bplaat/rescuebot/include/website.hpp

unsigned char src_website_html[] = {
  0x3c, 0x21, 0x44, 0x4f, 0x43, 0x54, 0x59, 0x50, 0x45, 0x20, 0x68, 0x74,
  0x6d, 0x6c, 0x3e, 0x0d, 0x0a, 0x3c, 0x68, 0x74, 0x6d, 0x6c, 0x20, 0x6c,
  0x61, 0x6e, 0x67, 0x3d, 0x22, 0x65, 0x6e, 0x22, 0x3e, 0x0d, 0x0a, 0x3c,
  0x68, 0x65, 0x61, 0x64, 0x3e, 0x0d, 0x0a, 0x20, 0x20, 0x20, 0x20, 0x3c,
  0x6d, 0x65, 0x74, 0x61, 0x20, 0x63, 0x68, 0x61, 0x72, 0x73, 0x65, 0x74,
  0x3d, 0x22, 0x55, 0x54, 0x46, 0x2d, 0x38, 0x22, 0x3e, 0x0d, 0x0a, 0x20,
  0x20, 0x20, 0x20, 0x3c, 0x6d, 0x65, 0x74, 0x61, 0x20, 0x6e, 0x61, 0x6d,
  0x65, 0x3d, 0x22, 0x76, 0x69, 0x65, 0x77, 0x70, 0x6f, 0x72, 0x74, 0x22,
  0x20, 0x63, 0x6f, 0x6e, 0x74, 0x65, 0x6e, 0x74, 0x3d, 0x22, 0x77, 0x69,
  0x64, 0x74, 0x68, 0x3d, 0x64, 0x65, 0x76, 0x69, 0x63, 0x65, 0x2d, 0x77,
  0x69, 0x64, 0x74, 0x68, 0x2c, 0x20, 0x69, 0x6e, 0x69, 0x74, 0x69, 0x61,
  0x6c, 0x2d, 0x73, 0x63, 0x61, 0x6c, 0x65, 0x3d, 0x31, 0x2e, 0x30, 0x2c,
  0x20, 0x6d, 0x69, 0x6e, 0x69, 0x6d, 0x75, 0x6d, 0x2d, 0x73, 0x63, 0x61,
  0x6c, 0x65, 0x3d, 0x31, 0x2e, 0x30, 0x2c, 0x20, 0x6d, 0x61, 0x78, 0x69,
  0x6d, 0x75, 0x6d, 0x2d, 0x73, 0x63, 0x61, 0x6c, 0x65, 0x3d, 0x31, 0x2e,
  0x30, 0x2c, 0x20, 0x75, 0x73, 0x65, 0x72, 0x2d, 0x73, 0x63, 0x61, 0x6c,
  0x61, 0x62, 0x6c, 0x65, 0x3d, 0x6e, 0x6f, 0x22, 0x3e, 0x0d, 0x0a, 0x20,
  0x20, 0x20, 0x20, 0x3c, 0x74, 0x69, 0x74, 0x6c, 0x65, 0x3e, 0x52, 0x65,
  0x73, 0x63, 0x75, 0x65, 0x42, 0x6f, 0x74, 0x3c, 0x2f, 0x74, 0x69, 0x74,
  0x6c, 0x65, 0x3e, 0x0d, 0x0a, 0x20, 0x20, 0x20, 0x20, 0x3c, 0x73, 0x74,
  0x79, 0x6c, 0x65, 0x3e, 0x0d, 0x0a, 0x20, 0x20, 0x20, 0x20, 0x20, 0x20,
  0x20, 0x20, 0x68, 0x74, 0x6d, 0x6c, 0x2c, 0x2e, 0x72, 0x6f, 0x6f, 0x74,
  0x7b, 0x68, 0x65, 0x69, 0x67, 0x68, 0x74, 0x3a, 0x31, 0x30, 0x30, 0x25,
  0x7d, 0x62, 0x6f, 0x64, 0x79, 0x7b, 0x6d, 0x61, 0x72, 0x67, 0x69, 0x6e,
  0x3a, 0x30, 0x3b, 0x68, 0x65, 0x69, 0x67, 0x68, 0x74, 0x3a, 0x31, 0x30,
  0x30, 0x25, 0x3b, 0x63, 0x6f, 0x6c, 0x6f, 0x72, 0x3a, 0x23, 0x31, 0x31,
  0x31, 0x3b, 0x62, 0x61, 0x63, 0x6b, 0x67, 0x72, 0x6f, 0x75, 0x6e, 0x64,
  0x2d, 0x63, 0x6f, 0x6c, 0x6f, 0x72, 0x3a, 0x23, 0x66, 0x66, 0x66, 0x3b,
  0x75, 0x73, 0x65, 0x72, 0x2d, 0x73, 0x65, 0x6c, 0x65, 0x63, 0x74, 0x3a,
  0x6e, 0x6f, 0x6e, 0x65, 0x3b, 0x63, 0x75, 0x72, 0x73, 0x6f, 0x72, 0x3a,
  0x64, 0x65, 0x66, 0x61, 0x75, 0x6c, 0x74, 0x7d, 0x0d, 0x0a, 0x20, 0x20,
  0x20, 0x20, 0x20, 0x20, 0x20, 0x20, 0x62, 0x6f, 0x64, 0x79, 0x2c, 0x62,
  0x75, 0x74, 0x74, 0x6f, 0x6e, 0x7b, 0x66, 0x6f, 0x6e, 0x74, 0x2d, 0x66,
  0x61, 0x6d, 0x69, 0x6c, 0x79, 0x3a, 0x2d, 0x61, 0x70, 0x70, 0x6c, 0x65,
  0x2d, 0x73, 0x79, 0x73, 0x74, 0x65, 0x6d, 0x2c, 0x42, 0x6c, 0x69, 0x6e,
  0x6b, 0x4d, 0x61, 0x63, 0x53, 0x79, 0x73, 0x74, 0x65, 0x6d, 0x46, 0x6f,
  0x6e, 0x74, 0x2c, 0x27, 0x53, 0x65, 0x67, 0x6f, 0x65, 0x20, 0x55, 0x49,
  0x27, 0x2c, 0x52, 0x6f, 0x62, 0x6f, 0x74, 0x6f, 0x2c, 0x4f, 0x78, 0x79,
  0x67, 0x65, 0x6e, 0x2c, 0x55, 0x62, 0x75, 0x6e, 0x74, 0x75, 0x2c, 0x43,
  0x61, 0x6e, 0x74, 0x61, 0x72, 0x65, 0x6c, 0x6c, 0x2c, 0x27, 0x4f, 0x70,
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
};
unsigned int src_website_html_len = 9247;
