bplaat/rescuebot/include/config.example.hpp

#include <Arduino.h>

// The ResueBots name
String rescuebot_name = "Unnamed";

// Enter here your WIFI SSID
String wifi_ssid = "";

// Enter here your WIFI password
String wifi_password = "";

// Activate extra serial debug info
#define DEBUG

// Activate the hall sensor code
#define ACTIVATE_HALL_SENSOR

// Hall sensor pin
#define HALL_SENSOR_PIN A0
